medukonis/cs437-final-project/ipaddress2string function.cpp

/*String IpAddress2String(const IPAddress& ipAddress)
{
  return String(ipAddress[0]) + String(".") +\
  String(ipAddress[1]) + String(".") +\
  String(ipAddress[2]) + String(".") +\
  String(ipAddress[3])  ; 
}*/
